glitchin-gitcord/WRO2023-TeamT.W.L_Public_Repository/schemes/18650 Batteries.png

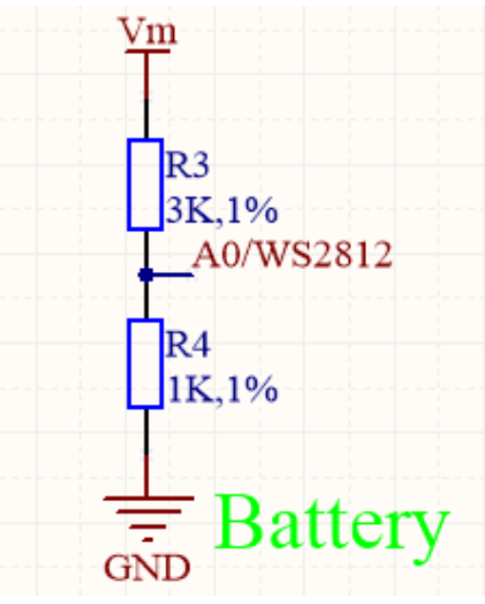
schemes/18650 Batteries.png
