glitchin-gitcord/WRO2023-TeamT.W.L_Public_Repository/t-photos/IMG_20230909_125841_790.jpg

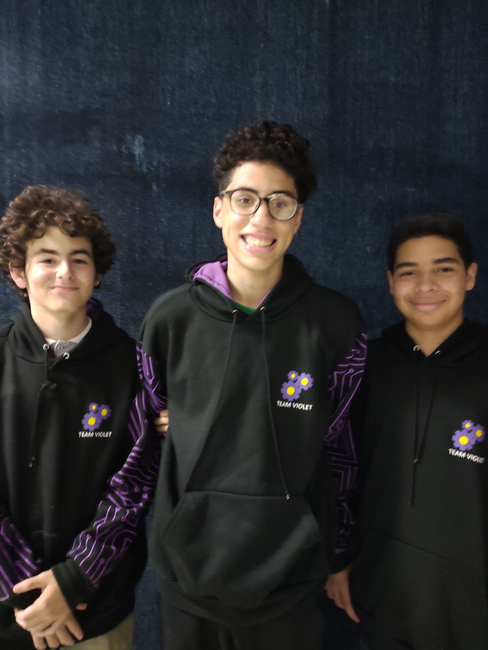
t-photos/IMG_20230909_125841_790.jpg
