glitchin-gitcord/WRO2023-TeamT.W.L_Public_Repository/t-photos/photo1694203656.jpeg

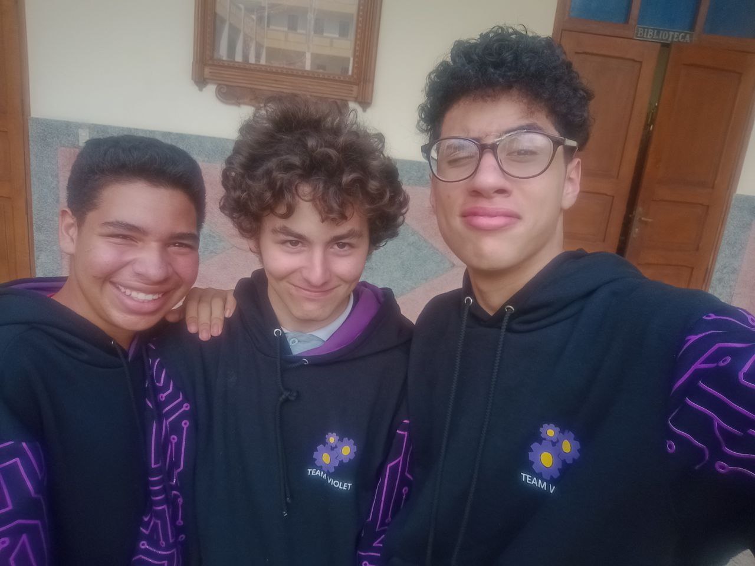
t-photos/photo1694203656.jpeg
