glitchin-gitcord/WRO2023-TeamT.W.L_Public_Repository/v-photos/bottom.jpeg

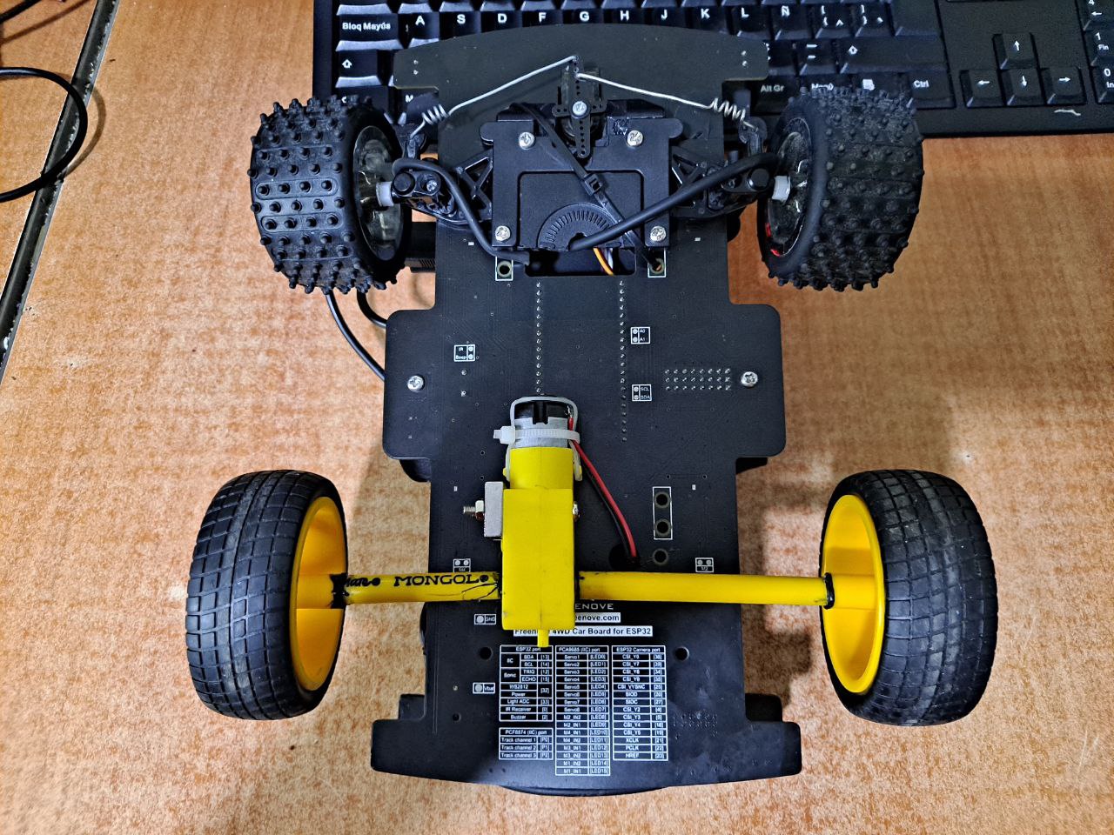
v-photos/bottom.jpeg
