glitchin-gitcord/WRO2023-TeamT.W.L_Public_Repository/v-photos/left side.jpeg

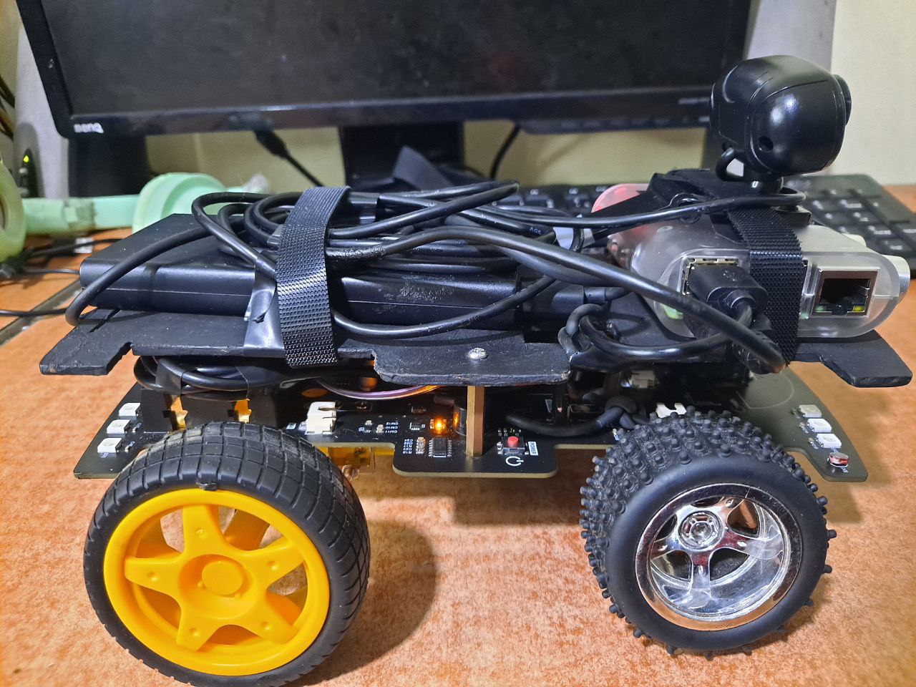
v-photos/left side.jpeg
