glitchin-gitcord/WRO2023-TeamT.W.L_Public_Repository/v-photos/right side.jpeg

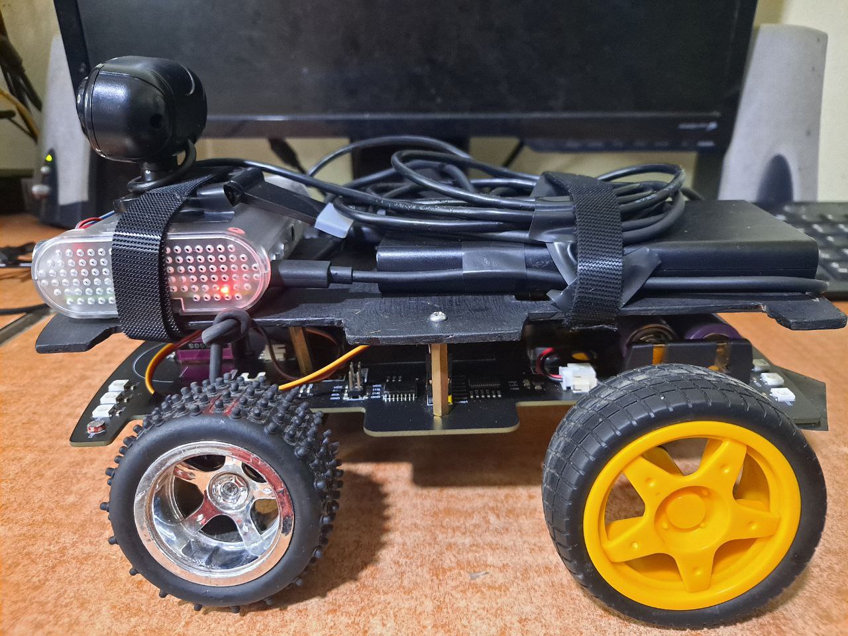
v-photos/right side.jpeg
