glitchin-gitcord/WRO2023-TeamT.W.L_Public_Repository/v-photos/top.jpeg

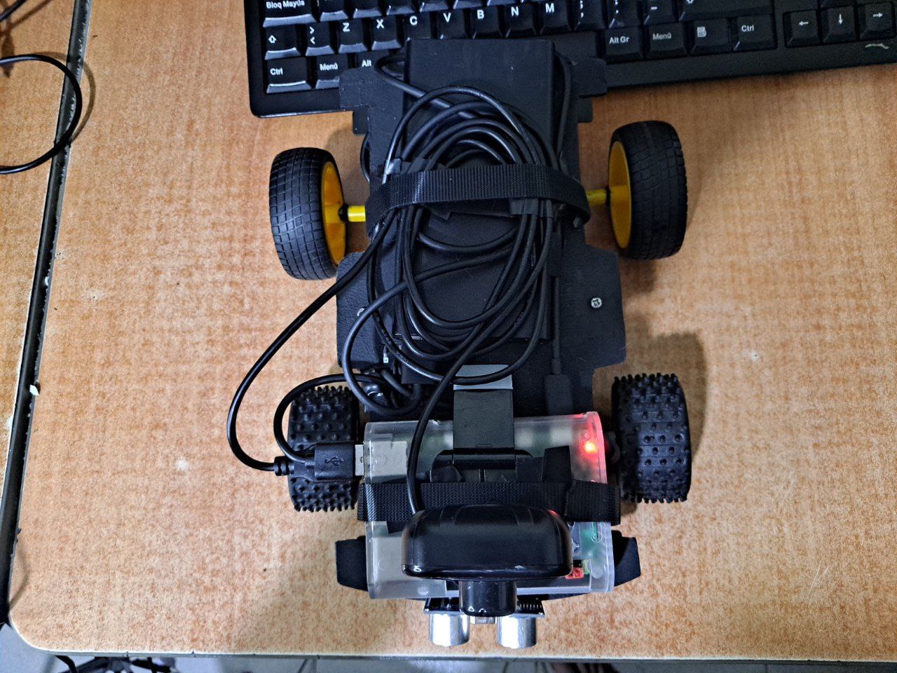
v-photos/top.jpeg
